kefcom/ps4adaptive/controller/controller c1931/images/IMG_0796.jpg

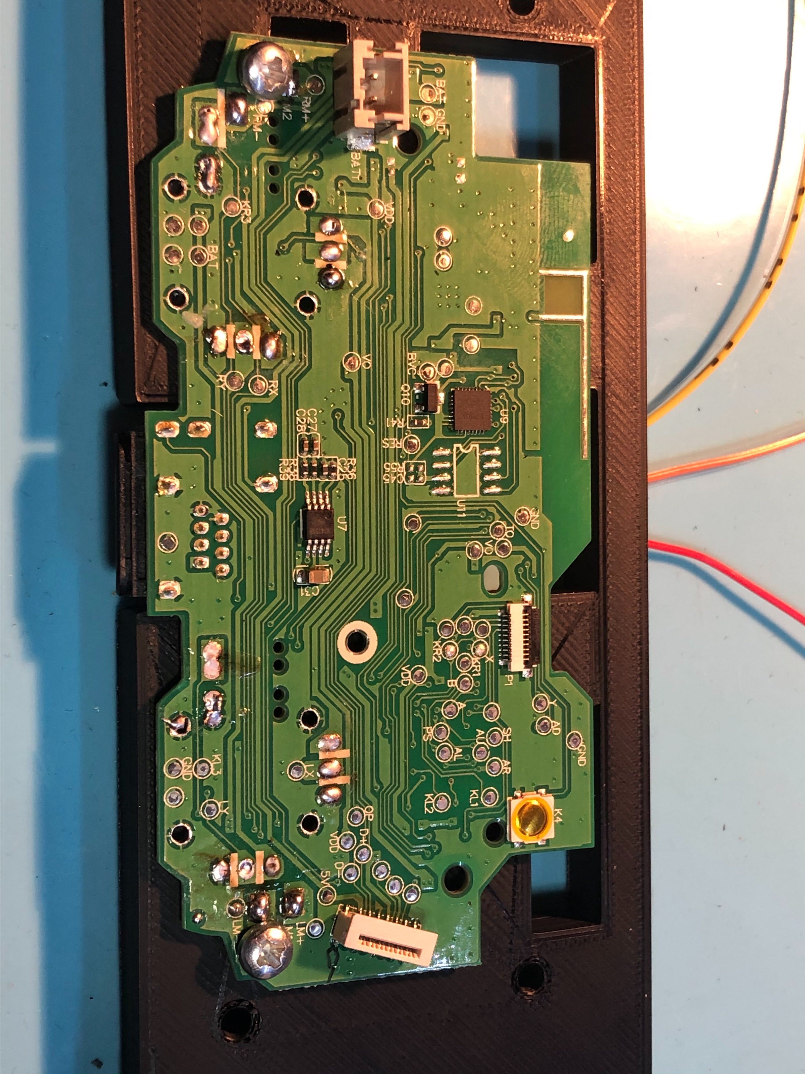
controller/controller c1931/images/IMG_0796.jpg
