kefcom/ps4adaptive/controller/controller c1931/images/Schematic_circle.png

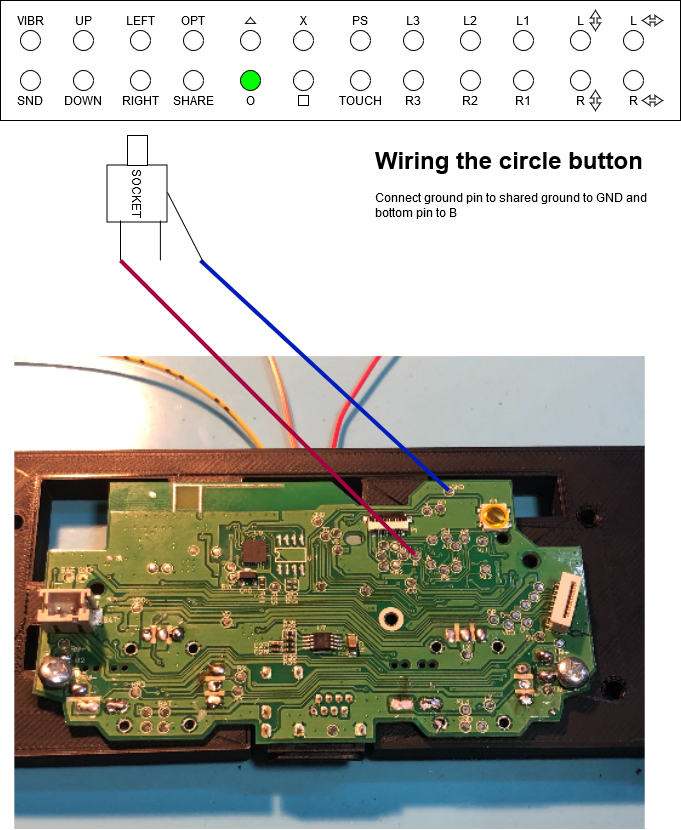
controller/controller c1931/images/Schematic_circle.png
