kefcom/ps4adaptive/controller/controller c1931/images/Schematic_left.png

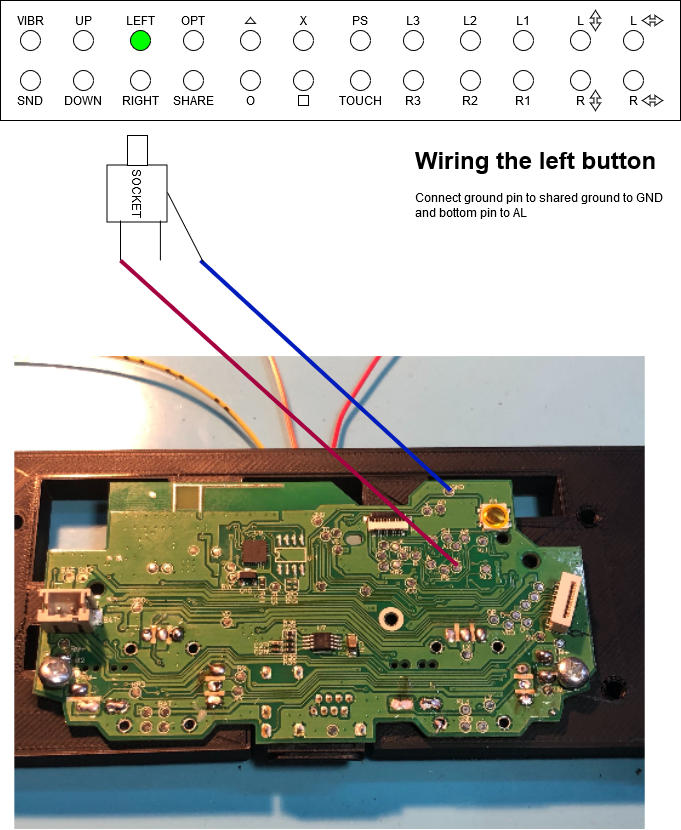
controller/controller c1931/images/Schematic_left.png
