kefcom/ps4adaptive/controller/controller c1931/images/Schematic_sharedground.png

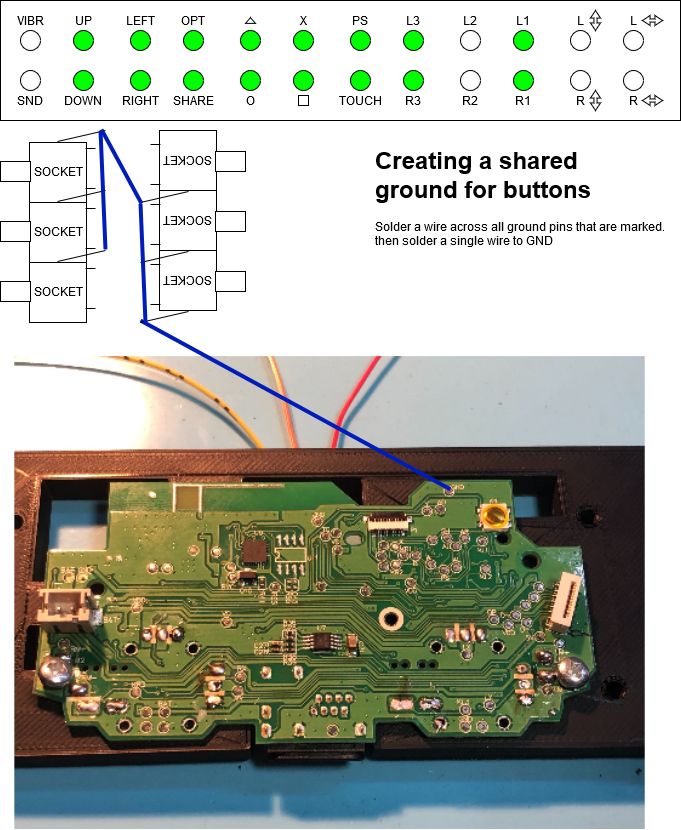
controller/controller c1931/images/Schematic_sharedground.png
