kefcom/ps4adaptive/controller/controller c1931/images/Schematic_speaker.png

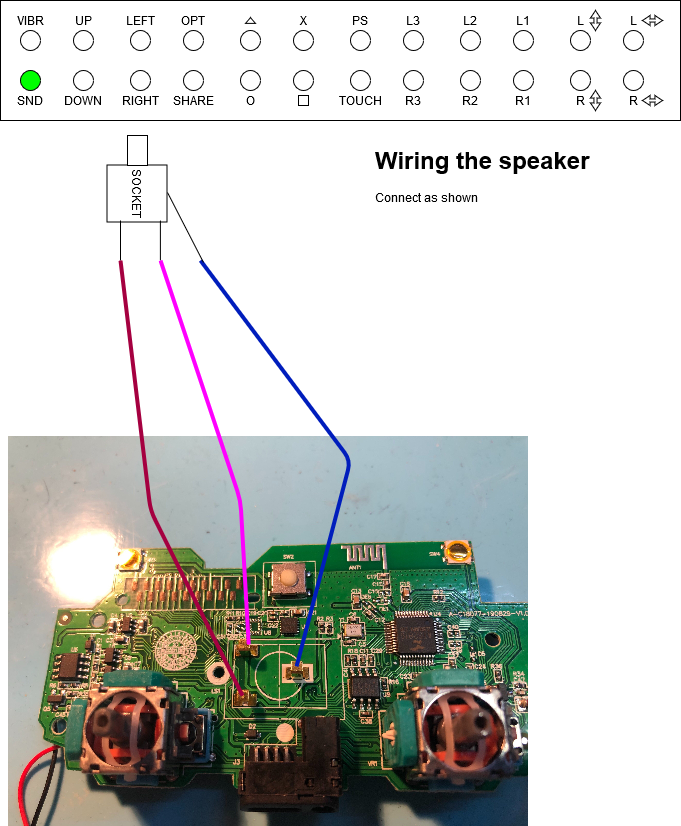
controller/controller c1931/images/Schematic_speaker.png
