kefcom/ps4adaptive/controller/controller c1931/images/Schematic_touch.png

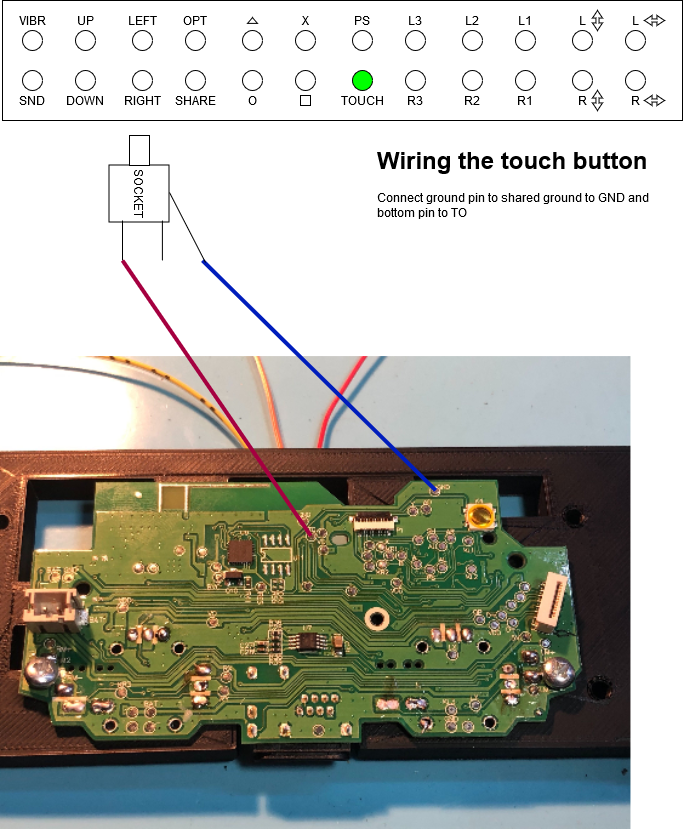
controller/controller c1931/images/Schematic_touch.png
