kefcom/ps4adaptive/controller/controller c1931/images/Schematic_up.png

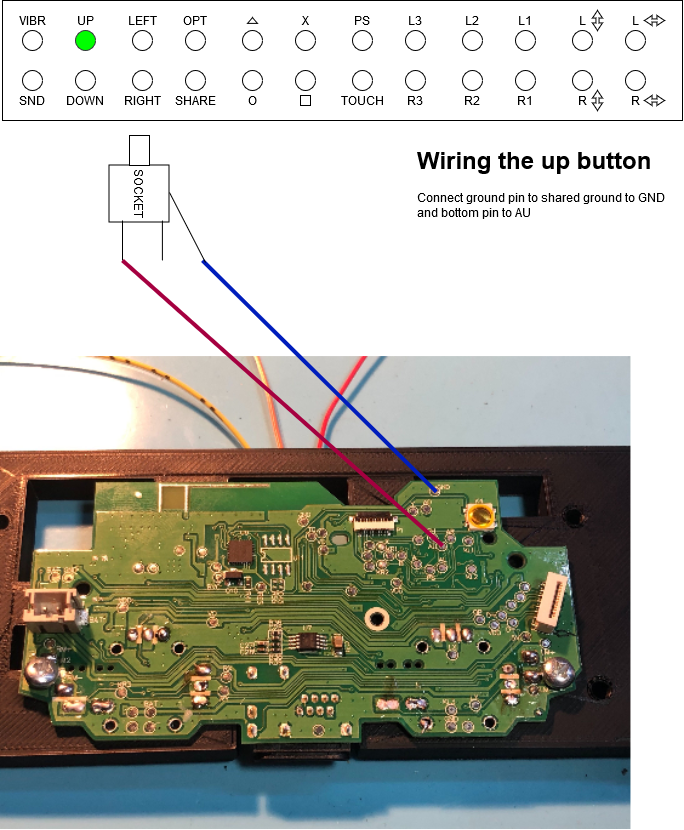
controller/controller c1931/images/Schematic_up.png
