kefcom/ps4adaptive/modules/1x arcadebutton/arcadebutton.jpg

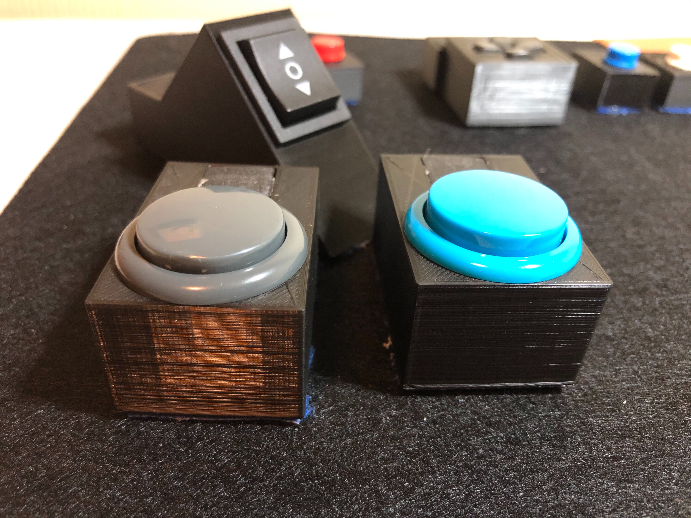
modules/1x arcadebutton/arcadebutton.jpg
