kefcom/ps4adaptive/modules/1x d-pad/d-pad.jpg

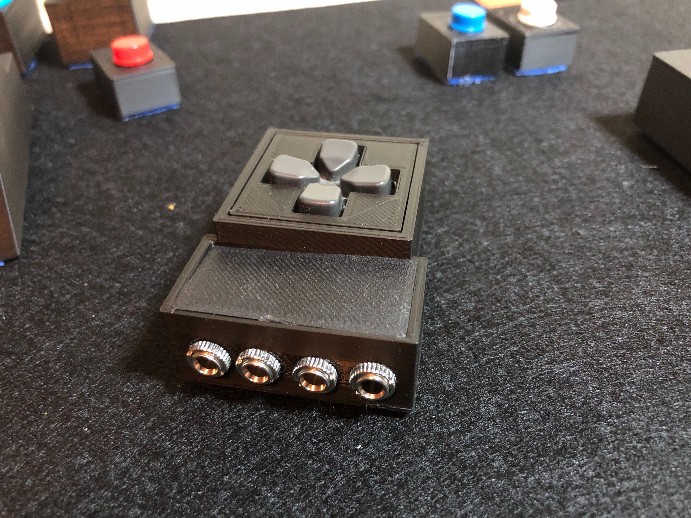
modules/1x d-pad/d-pad.jpg
