kefcom/ps4adaptive/modules/1x keyboard/1xkeyboard.jpg

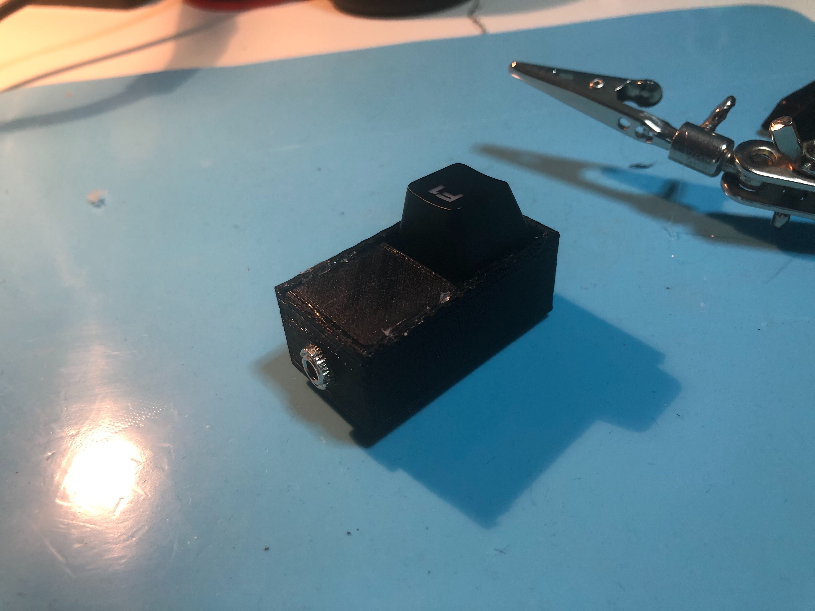
modules/1x keyboard/1xkeyboard.jpg
