kefcom/ps4adaptive/modules/1x rockerswitch on-off-on/rockerswitch.jpg

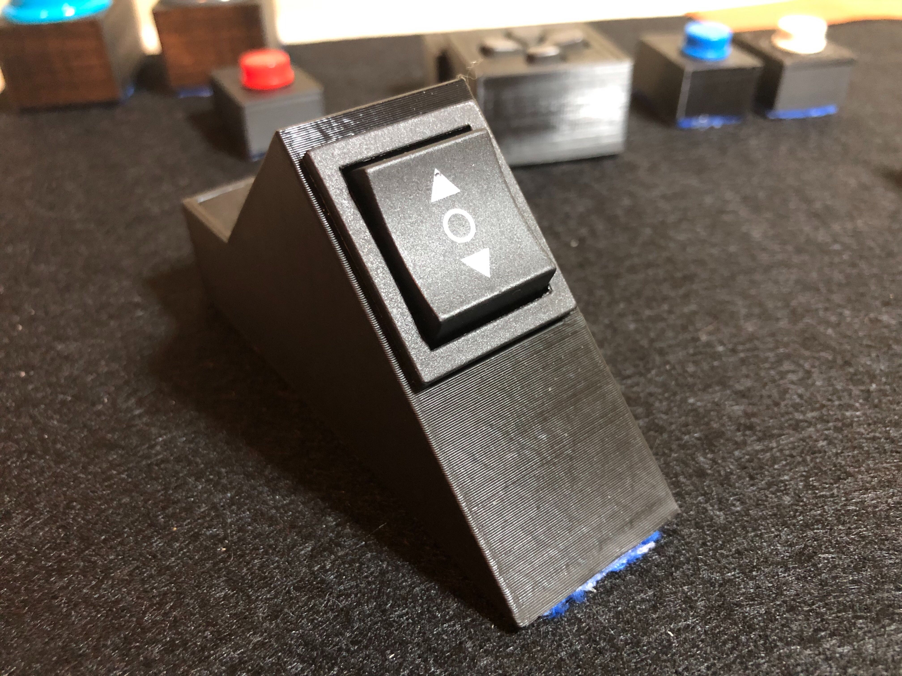
modules/1x rockerswitch on-off-on/rockerswitch.jpg
