kefcom/ps4adaptive/modules/1x simple button with tactile feedback/singlebutton.jpg

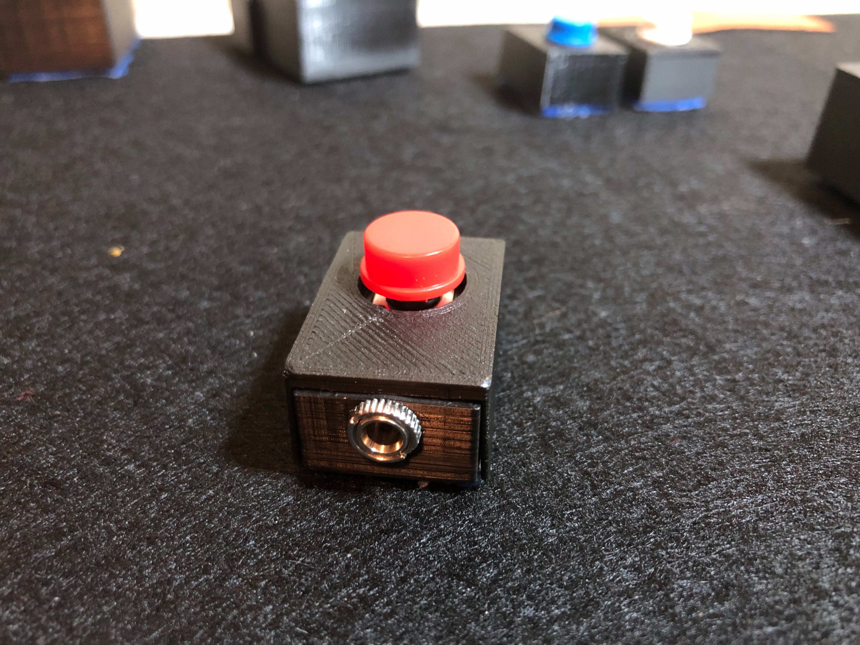
modules/1x simple button with tactile feedback/singlebutton.jpg
