kefcom/ps4adaptive/modules/4x button/4xbutton.jpg

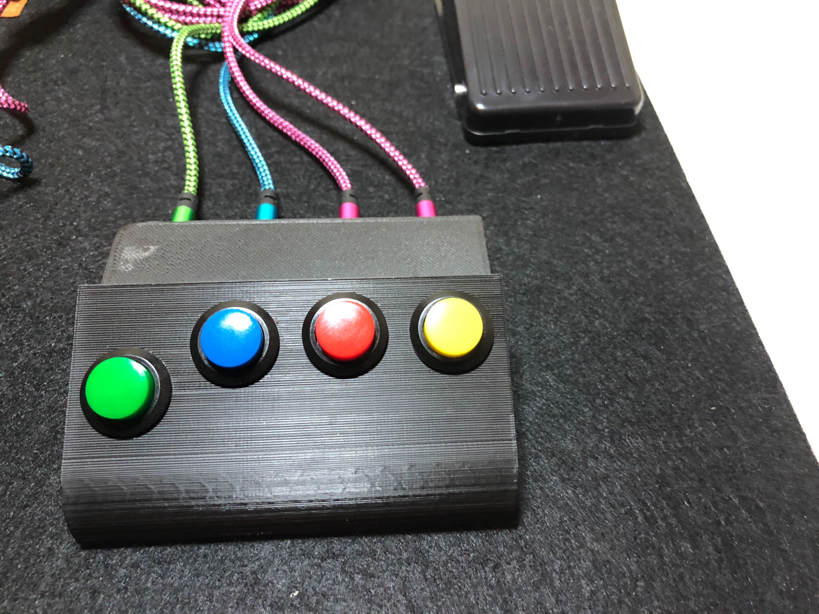
modules/4x button/4xbutton.jpg
