kefcom/ps4adaptive/modules/6x keyboard/6x keyboard.jpg

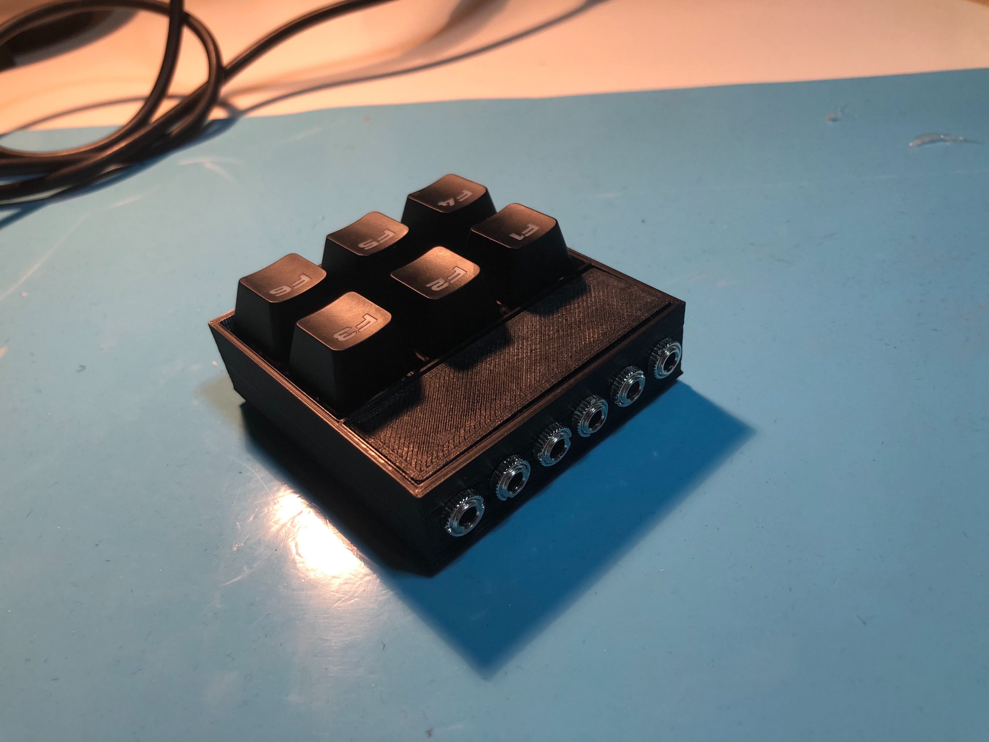
modules/6x keyboard/6x keyboard.jpg
