kefcom/ps4adaptive/modules/footpedal/footpedal.jpg

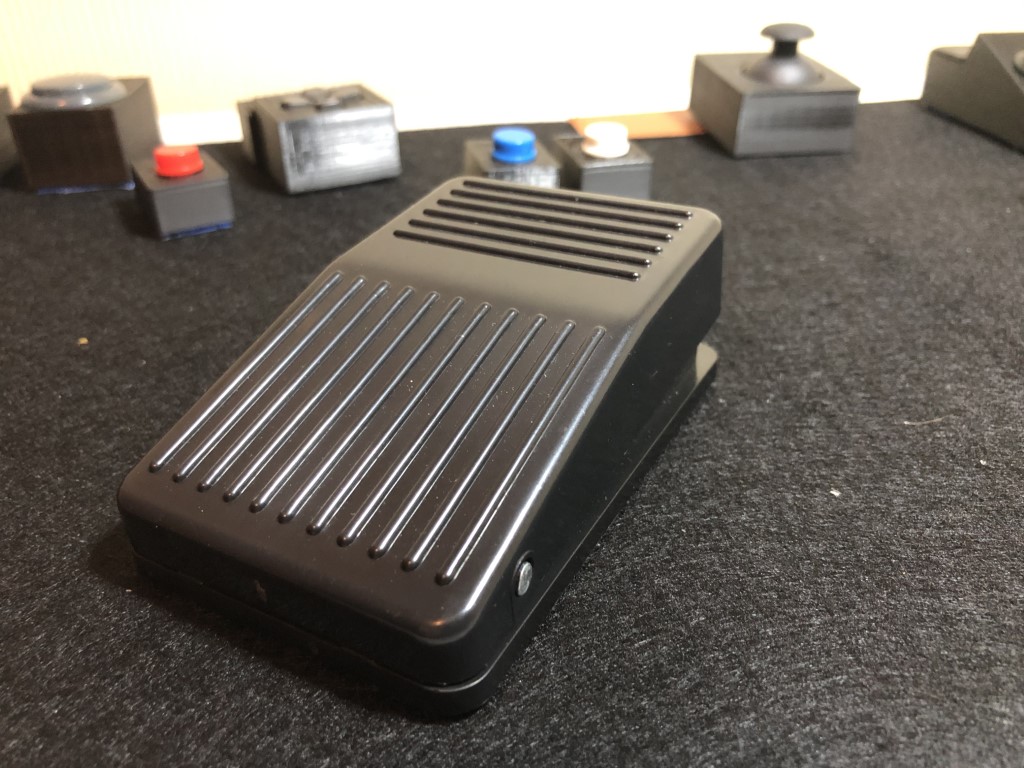
modules/footpedal/footpedal.jpg
