kefcom/ps4adaptive/modules/joystick with click/joystick.jpg

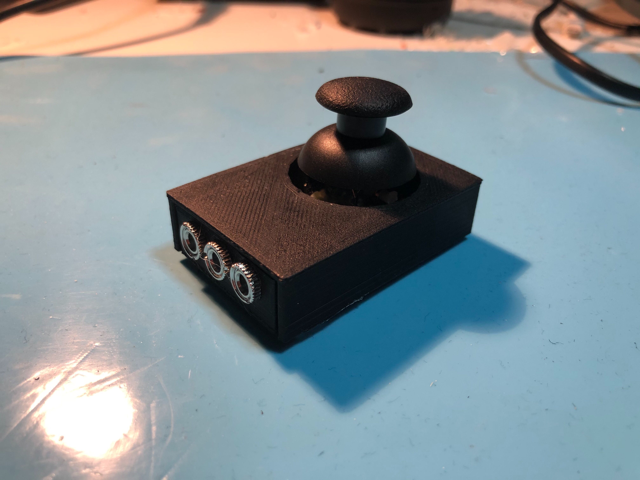
modules/joystick with click/joystick.jpg
