kefcom/ps4adaptive/modules/vibrator/vibrator.jpg

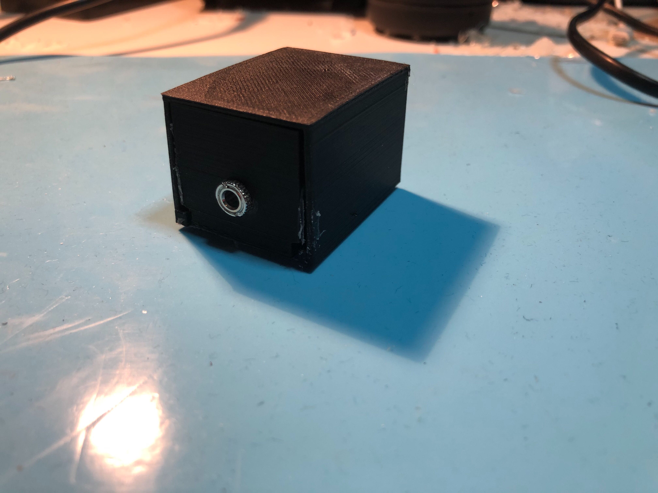
modules/vibrator/vibrator.jpg
